Tinkerforge/performance-dc-bricklet/software/examples/mathematica/ExampleConfiguration.nb.txt

Needs["NETLink`"]
LoadNETAssembly["Tinkerforge",NotebookDirectory[]<>"../../.."]

host="localhost"
port=4223
uid="XYZ"(*Change XYZ to the UID of your Performance DC Bricklet*)

(*Create IPConnection and device object*)
ipcon=NETNew["Tinkerforge.IPConnection"]
pdc=NETNew["Tinkerforge.BrickletPerformanceDC",uid,ipcon]
ipcon@Connect[host,port]

pdc@SetDriveMode[Tinkerforge`BrickletPerformanceDC`DRIVEUMODEUDRIVEUCOAST]
pdc@SetPWMFrequency[10000](*Use PWM frequency of 10 kHz*)
pdc@SetMotion[4096,4096](*Slow ac-/deceleration (12.5 %/s)*)
pdc@SetVelocity[32767](*Full speed forward (100 %)*)
pdc@SetEnabled[True](*Enable motor power*)

Input["Click OK to exit"]

(*Stop motor before disabling motor power*)
pdc@SetMotion[4096,16384](*Fast decceleration (50 %/s) for stopping*)
pdc@SetVelocity[0](*Request motor stop*)
Pause[2](*Wait for motor to actually stop: velocity (100 %) / decceleration (50 %/s) = 2 s*)
pdc@SetEnabled[False](*Disable motor power*)

ipcon@Disconnect[]
ReleaseNETObject[pdc]
ReleaseNETObject[ipcon]
